Xerolux/idm-room-sensor/docs/concepts/fail-safe.md

# Fail Safe

On communication failure use local sensors, conservative values and cooling inhibit.

## Status

- [ ] Reviewed
- [ ] Bench tested
- [ ] Real-device tested
