Xerolux/idm-room-sensor/docs/concepts/sensor-fusion.md

# Sensor Fusion

Reject stale or implausible data before median, weighted or quality-based aggregation.

## Status

- [ ] Reviewed
- [ ] Bench tested
- [ ] Real-device tested
