Xerolux/idm-room-sensor/docs/hardware/connector-pinout.md

# Connector Pinout

Use keyed, labelled connectors and verify every terminal against the installation diagram.

## Status

- [ ] Reviewed
- [ ] Bench tested
- [ ] Real-device tested
