Xerolux/idm-room-sensor/docs/hardware/humidity-output.md

# Humidity Output

A precision DAC and 24 V-capable op amp generate the analog humidity signal.

## Status

- [ ] Reviewed
- [ ] Bench tested
- [ ] Real-device tested
