Xerolux/idm-room-sensor/docs/hardware/kty-emulation.md

# Kty Emulation

A switched precision-resistor ladder is safer than exposing a low-voltage digital pot to an unknown input.

## Status

- [ ] Reviewed
- [ ] Bench tested
- [ ] Real-device tested
