Xerolux/idm-room-sensor/docs/hardware/pipe-sensor.md

# Pipe Sensor

The pipe module measures pipe temperature and accepts an independent condensation contact.

## Status

- [ ] Reviewed
- [ ] Bench tested
- [ ] Real-device tested
