Xerolux/idm-room-sensor/docs/hardware/power-input.md

# Power Input

Target 14–30 V DC with reverse protection, TVS, filtering and a wide-input buck regulator.

## Status

- [ ] Reviewed
- [ ] Bench tested
- [ ] Real-device tested
