Xerolux/idm-room-sensor/hardware/fake-sensor/DESIGN_STATUS.md

# fake-sensor

- [x] Architecture
- [x] Connector concept
- [x] Power tree
- [x] Test points
- [ ] Peer review
- [ ] Routed PCB
- [ ] Prototype
- [ ] Validation
