Xerolux/idm-room-sensor/ROADMAP.md

# Roadmap

## Milestone 1 — Characterization
Original sensor and IDM input measurements.

## Milestone 2 — Bench prototype
Validated 0–10 V and KTY stages.

## Milestone 3 — Software integration
Upstream `set_external_climate`, CI and stale-value diagnostics.

## Milestone 4 — Controlled cooling test
Independent pipe guard, logged commissioning and fault injection.

## Milestone 5 — Fabrication release
Reviewed KiCad design, Gerber/BOM/CPL and tagged hardware release.
