Xerolux/idm-room-sensor/wiki/_Sidebar.md

* [[Home]]
* [[Architecture]]
* [[Original-Sensor]]
* [[Hardware-ESP-Sensor]]
* [[Hardware-Classic-Sensor]]
* [[Hardware-Fake-Sensor]]
* [[Climate-Engine]]
* [[Home-Assistant]]
* [[Esphome]]
* [[Mqtt]]
* [[Native-ESP-IDF]]
* [[KNX]]
* [[Modbus-GLT]]
* [[Cooling-Safety]]
* [[Calibration]]
* [[Calibration-Storage]]
* [[Source-Quality]]
* [[State-Machine]]
* [[Watchdog]]
* [[Validation]]
* [[Ordering]]
* [[FAQ]]
* [[Troubleshooting]]
* [[Roadmap]]
