Xerolux/idm-room-sensor/wiki/Esphome.md

# Esphome

See `docs/protocols/esphome.md`.

- [x] Supported manifests and representative images compile tested
- [x] MQTT, local web UI and diagnostic contracts tested
- [ ] Hardware bench tested
- [ ] Real-device tested
- [ ] Community reviewed
