Xerolux/idm-room-sensor/wiki/Mqtt.md

# Mqtt

See `docs/protocols/mqtt.md`.

- [x] Discovery, availability and JSON payload contracts tested
- [x] ESPHome configurations compile tested
- [ ] Broker-loss bench tested
- [ ] Real-device tested
- [ ] Community reviewed
