Xerolux/idm-room-sensor/wiki/Roadmap.md

# Roadmap

Milestones from prototype to validated release.

> Status: Work in progress. Contributions and measurements are welcome.

The locally executable Home Assistant and firmware backlog through FW-08 is
implemented and automatically tested. The current critical path is the
original-sensor/IDM input characterization, external hardware review,
prototype manufacture and physical validation listed in `TASKS.md`.
