Xerolux/idm-room-sensor/wiki/Source-Quality.md

# Source Quality

See `docs/firmware/source-quality.md`.

- [x] Range, finite-value, age, wraparound and minimum-quality paths tested
- [x] Used by MQTT, Home Assistant and native REST inputs
- [ ] Hardware fault-injection tested
- [ ] Real-device tested
- [ ] Community reviewed
