Xerolux/idm-room-sensor/wiki/State-Machine.md

# State Machine

See `docs/firmware/state-machine.md`.

- [x] Bridge transitions, stale fallback and output-fault recovery unit tested
- [x] Shared by ESPHome and native ESP-IDF targets
- [ ] Hardware fault-injection tested
- [ ] Real-device tested
- [ ] Community reviewed
