Xerolux/idm-room-sensor/wiki/Watchdog.md

# Watchdog

See `docs/firmware/watchdog.md`.

- [x] Native ESP-IDF watchdog and brownout configuration build tested
- [x] Fail-safe output is attempted before networking
- [ ] Blocked-task, brownout and long-term fault injection
- [ ] Real-device tested
- [ ] Community reviewed
