Xerolux/idm-room-sensor/docs/help-wanted.md

# Community help wanted

We need:
- LCN-FTW04 owners who can provide non-destructive voltage/resistance measurements.
- IDM ALM/Navigator owners with resistance-decade equipment.
- KiCad reviewers experienced in mixed-signal 0–10 V outputs and switch-mode supplies.
- ESPHome developers to compile and test the custom components.
- HVAC professionals to review condensation and hydraulic safety assumptions.

Use the measurement issue template and include device model, firmware, instrument, wiring and ambient conditions.
