Xerolux/idm-room-sensor/docs/original-sensor.md

# Originalsensor LCN-FTW04

Quelle: IDM-Montageanleitung **Raum-Feuchtesensor LCN-FTW04**, Art.-Nr. **191275**, Ausgabe 09.09.2015.

## Anschluss

| Sensor-Pin | Bezeichnung | IDM-Klemme |
|---:|---|---:|
| 2 | KTY-Temperatursensor | 43 |
| 3 | KTY-Rückleiter | 41 |
| 5 | Out RH 0–10 V | 40 |
| 6 | GND | 41 |
| 7 | 14–32 V DC | 42 |

Es werden vier Leitungen zur IDM benötigt, da Sensor-Pin 3 und 6 gemeinsam auf Klemme 41 liegen.

Es kann nur ein Raum-Feuchtesensor an die Navigator-Regelung angeschlossen werden. Für weitere Räume verwendet die Regelung die Temperaturen der jeweiligen Raumgeräte zusammen mit der Feuchte des Referenzraums.
