Xerolux/idm-room-sensor/docs/repository-settings.md

# Empfohlene Repository-Einstellungen

**Beschreibung**

> Open hardware temperature and humidity sensors plus a Home Assistant sensor simulator for IDM AERO ALM / Navigator 2.0.

**Topics**

`idm` `heat-pump` `home-assistant` `esphome` `esp32` `kicad` `humidity-sensor` `temperature-sensor` `open-hardware` `aero-alm`

**Features**

- Issues aktivieren
- Discussions aktivieren
- Wiki optional aktivieren
- Branch Protection für `main`
- Squash Merge bevorzugen
