Xerolux/idm-room-sensor/pages/_navbar.md

* [GitHub](https://github.com/Xerolux/IDM-Smart-Climate-Platform)
* [idm-heatpump-hass](https://github.com/Xerolux/idm-heatpump-hass)
