Xerolux/idm-room-sensor/pages/cooling-safety.md

# Cooling Safety

Never depend exclusively on Wi-Fi, Home Assistant or KNX for condensation protection. Install an independent pipe-mounted dew-point switch that can inhibit cooling.
