Xerolux/idm-room-sensor/pages/help-wanted.md

# Help Wanted

Needed: owners of LCN-FTW04 sensors, resistance-decade measurements of IDM inputs, KiCad review, ESPHome compilation tests and supervised cooling commissioning.
