Xerolux/idm-room-sensor/wiki/Home.md

# Home

Project overview, supported concepts and current maturity.

> Status: Work in progress. Contributions and measurements are welcome.
