Xerolux/idm-room-sensor/wiki/Modbus-GLT.md

# Modbus GLT

External room temperature and humidity registers and ownership rules.

> Status: Work in progress. Contributions and measurements are welcome.
