Xerolux/idm-room-sensor/wiki/Original-Sensor.md

# Original Sensor

Known LCN-FTW04 information and open electrical questions.

> Status: Work in progress. Contributions and measurements are welcome.
