Xerolux/idm-room-sensor/wiki/Pipe-Sensor.md

# Pipe Sensor

See `docs/hardware/pipe-sensor.md`.

- [ ] Community reviewed
- [ ] Validated
