Xerolux/idm-room-sensor/wiki/Power-Input.md

# Power Input

See `docs/hardware/power-input.md`.

- [ ] Community reviewed
- [ ] Validated
