Xerolux/idm-room-sensor/wiki/Sensor-Fusion.md

# Sensor Fusion

See `docs/concepts/sensor-fusion.md`.

- [ ] Community reviewed
- [ ] Validated
