Xerolux/idm-room-sensor/docs/adr/ADR-001-mcu.md

# Decision: ESP32-C3-MINI-1

Wi-Fi, ESPHome and compact certified module.

Status: proposed, hardware review required.
