Xerolux/idm-room-sensor/docs/adr/ADR-002-humidity-sensor.md

# Decision: SHT45

Mature, accurate digital humidity sensor.

Status: proposed, hardware review required.
