Xerolux/idm-room-sensor/docs/adr/ADR-003-dac.md

# Decision: MCP4725

Simple 12-bit I²C DAC; final accuracy requires calibration.

Status: proposed, hardware review required.
