Xerolux/idm-room-sensor/docs/adr/ADR-004-opamp.md

# Decision: OPA197

High supply rating suitable for 0–10 V.

Status: proposed, hardware review required.
