Xerolux/idm-room-sensor/docs/adr/ADR-005-power.md

# Decision: Wide-input buck regulator

Final choice follows availability and layout review.

Status: proposed, hardware review required.
