Xerolux/idm-room-sensor/docs/adr/ADR-006-temp-emulation.md

# Decision: Switched resistor ladder

Safer against unknown excitation than a direct digital pot.

Status: proposed, hardware review required.
