Xerolux/idm-room-sensor/docs/adr/ADR-007-pipe-sensor.md

# Decision: PT1000 or DS18B20

PT1000 for robust installations, DS18B20 for prototypes.

Status: proposed, hardware review required.
