Xerolux/idm-room-sensor/docs/home-assistant/helpers.md

# Helpers

Suggested helpers cover strategy, fallbacks, timeout, margin, inhibit and heating circuit.

## Status

- [ ] Reviewed
- [ ] Bench tested
- [ ] Real-device tested
