Xerolux/idm-room-sensor/docs/home-assistant/strategy-max-humidity.md

# Strategy Max Humidity

Forward maximum humidity together with temperature from the same room.

## Status

- [ ] Reviewed
- [ ] Bench tested
- [ ] Real-device tested
