Xerolux/idm-room-sensor/docs/home-assistant/strategy-weighted.md

# Strategy Weighted

Weights can reflect cooled area or known moisture load and must be documented.

## Status

- [ ] Reviewed
- [ ] Bench tested
- [ ] Real-device tested
