Xerolux/idm-room-sensor/docs/protocols/analog-interface.md

# Analog Interface

The original interface combines supply, common, 0–10 V humidity and passive KTY temperature.

## Status

- [ ] Reviewed
- [ ] Bench tested
- [ ] Real-device tested
