Xerolux/idm-room-sensor/docs/protocols/knx.md

# Knx

KNX values can be imported into Home Assistant and forwarded through GLT or the analog bridge.

## Status

- [ ] Reviewed
- [ ] Bench tested
- [ ] Real-device tested
