Xerolux/idm-room-sensor/docs/protocols/modbus-tcp.md

# Modbus Tcp

Use known register definitions and model capability checks instead of arbitrary raw writes.

## Status

- [ ] Reviewed
- [ ] Bench tested
- [ ] Real-device tested
