Xerolux/idm-room-sensor/docs/cooling-safety.md

# Kühlung und Kondensationsschutz

Die Softwareberechnung ist eine Komfort- und Regelungsebene, aber kein alleiniger Sicherheitsschutz.

Empfohlene Ebenen:

1. Raumtemperatur und Feuchte je Raum erfassen.
2. Taupunkt und Taupunktabstand berechnen.
3. Kritischsten Raum an die IDM melden.
4. Unabhängigen Taupunktwächter direkt am blanken Vorlaufrohr montieren.
5. Dessen potentialfreien Kontakt auf den vorgesehenen Taupunkt-/Kühlsperreingang der IDM legen.

Bei HA-, KNX- oder WLAN-Ausfall müssen konservative Ersatzwerte oder lokale Sensoren übernehmen.
