Xerolux/idm-room-sensor/docs/safety.md

# Sicherheit und Validierung

## Vor dem Anschluss zwingend prüfen

1. Spannung zwischen IDM-Klemme 42 und 43.
2. Feuchteeingang an Klemme 40 gegen Klemme 41.
3. Messspannung und Messstrom am KTY-Eingang Klemme 43 gegen Klemme 41.
4. Kennlinie eines echten KTY81-210 an der IDM.
5. Kennlinie des originalen Feuchteausgangs.
6. Massebezug der Analogsignale.
7. Verhalten bei Leitungsbruch, Neustart und WLAN-Ausfall.

## Kühlbetrieb

Ein Softwarewert aus Home Assistant darf nicht die einzige Schutzmaßnahme gegen Kondensation sein. Ein unabhängiger Taupunktwächter am Heiz-/Kühlkreis sollte bestehen bleiben.

## Produktionsstatus

Die Dateien sind Entwicklungsunterlagen. Es liegen noch keine EMV-, Sicherheits-, Temperatur- oder Langzeittests vor.
