Xerolux/idm-room-sensor/docs/ordering/alternatives.md

# Alternatives

Substitutions must match electrical limits, package, footprint and temperature grade.

## Status

- [ ] Reviewed
- [ ] Bench tested
- [ ] Real-device tested
