Xerolux/idm-room-sensor/docs/ordering/prototype-order.md

# Prototype Order

Order small quantities until footprints and behavior are verified.

## Status

- [ ] Reviewed
- [ ] Bench tested
- [ ] Real-device tested
