Xerolux/idm-room-sensor/hardware/classic-sensor/enclosure/PRINTING.md

PETG/ASA, 0,20 mm, 3–4 Perimeter, ohne Support. Außenmaß ca. 45.0 × 35.0 × 20.0 mm.
