Xerolux/idm-room-sensor/hardware/esp-sensor/enclosure/PRINTING.md

PETG/ASA, 0,20 mm, 3–4 Perimeter, ohne Support. Außenmaß ca. 65.0 × 45.0 × 20.0 mm.
