Xerolux/idm-room-sensor/hardware/fake-sensor/enclosure/PRINTING.md

PETG/ASA, 0,20 mm, 3–4 Perimeter, ohne Support. Außenmaß ungefähr 71 × 49 × 22 mm.
