Xerolux/idm-room-sensor/hardware/fake-sensor/fabrication/README.md

# Fabrication status

Development templates only; not released for ordering.
