Xerolux/idm-room-sensor/docs/hardware/test-points.md

# Test Points

Expose 24 V, 5 V, 3.3 V, DAC, 0–10 V, I²C, UART and temperature terminals.

## Status

- [ ] Reviewed
- [ ] Bench tested
- [ ] Real-device tested
