Xerolux/idm-room-sensor/docs/validation/fail-safe-test.md

# Fail Safe Test

Disconnect each dependency and verify conservative output and alarm.

## Status

- [ ] Reviewed
- [ ] Bench tested
- [ ] Real-device tested
