Xerolux/idm-room-sensor/docs/validation/idm-input-test.md

# Idm Input Test

Measure open-circuit conditions and map resistance to displayed temperature with a decade box.

## Status

- [ ] Reviewed
- [ ] Bench tested
- [ ] Real-device tested
