Xerolux/idm-room-sensor/docs/validation/original-sensor-test.md

# Original Sensor Test

Measure current and output at multiple stable humidity points with a reference.

## Status

- [ ] Reviewed
- [ ] Bench tested
- [ ] Real-device tested
