Xerolux/idm-room-sensor/docs/validation/thermal-test.md

# Thermal Test

Test at minimum and maximum supply voltage until thermal equilibrium.

## Status

- [ ] Reviewed
- [ ] Bench tested
- [ ] Real-device tested
