Xerolux/idm-room-sensor/hardware/fake-sensor/TEST_PLAN.md

# fake-sensor test plan

1. Inspect.
2. Current-limited power-up at 14 V.
3. Repeat at 24 V and 30 V.
4. Verify outputs and fail-safe.
5. Save raw data.
