Xerolux/idm-room-sensor/validation/protocols/power-input.md

# Power Input test

Status: NOT RUN

1. Record revisions and equipment.
2. Execute controlled test.
3. Save raw data and photos.
4. Compare with criteria.
